scott-vincent/radio-panel/radio-panel/radio.h

#ifndef _RADIO_H_
#define _RADIO_H_

#include "simvars.h"
#include "sevensegment.h"

class radio
{
private:
    SimVars* simVars;
    Aircraft loadedAircraft = UNDEFINED;
    bool airliner = false;
    sevensegment* sevenSegment;

    unsigned char display1[8];
    unsigned char display2[8];
    unsigned char display3[8];
    double activeFreq;
    double standbyFreq;
    int tcasMode = -1;
    int lastTcasMode = -1;
    int transponderState = -1;
    int lastTransponderState = -1;
    int squawk = 0;
    bool showNav = false;
    int usingNav = 0;              // 0 = NAV1, 1 = NAV2, 2 = ADF
    int spoilersVal = INT_MIN;
    int spoilersAutoVal = -6;       // Default to spoilers = retracted
    int spoilersDownVal = 14;
    int lastSpoilersPos = -1;       // 0 = auto, 1 = retracted, 2 = half, 3 = full
    bool gearDown = true;
    bool showSeatBelts = false;
    int receiveAllHideDelay = 0;
    int audioNav1 = 0;
    int audioNav2 = 0;
    int audioAdf = 0;

    // Hardware controls
    int freqWholeControl = -1;
    int freqFracControl = -1;
    int swapControl = -1;
    int comControl = -1;
    int navControl = -1;
    int squawkControl = -1;
    int trimWheelControl = -1;
    int spoilersAutoControl = -1;
    int spoilersPosControl = -1;
    int spoilersDownControl = -1;
    int gearUpControl = -1;
    int gearDownControl = -1;
    int seatBeltsControl = -1;
    int delayedAdfSwap = 0;

    int prevFreqWholeVal = 0;
    int prevFreqFracVal = 0;
    int prevFreqFracPush = 0;
    int fracSetSel = 0;
    int prevSwapPush = 0;
    int prevComPush = 0;
    int prevNavPush = 0;
    int prevSquawkVal = 0;
    int prevSquawkPush = 0;
    int squawkSetSel = 0;
    int prevTrimWheelVal = 0;
    int prevSpoilersAutoToggle = -1;
    int prevSpoilersDownToggle = -1;
    int prevGearUpToggle = -1;
    int prevGearDownToggle = -1;
    int prevFreqWholeValSb;
    int prevFreqFracValSb;
    int prevFreqFracPushSb;
    int prevSwapPushSb = 0;
    int prevComPushSb = 0;
    int prevNavPushSb = 0;
    int prevSquawkValSb = 0;
    int prevSquawkPushSb = 0;

    time_t lastFreqAdjust = 0;
    time_t lastFreqPush = 0;
    time_t lastSquawkAdjust = 0;
    time_t lastSquawkPush = 0;
    time_t lastTcasAdjust = 0;
    time_t now;

public:
    radio();
    void render();
    void update();

private:
    void blankDisplays();
    void writeCom(unsigned char* display, double freq);
    void writeNav(unsigned char* display, double freq);
    void writeAdf(unsigned char* display, double freq);
    void addGpio();
    void gpioFreqWholeInput();
    void gpioFreqFracInput();
    void gpioButtonsInput();
    void gpioSquawkInput();
    void gpioTrimWheelInput();
    void gpioSpoilersInput();
    void gpioGearInput();
    double adjustComWhole(int adjust);
    double adjustComFrac(int adjust);
    double adjustNavWhole(int adjust);
    double adjustNavFrac(int adjust);
    int adjustAdf(double val, int adjust, int setSel);
    int adjustDigit(int val, int adjust);
    int adjustHalfDigit(int val, int adjust);
    int adjustSquawk(int adjust);
    int adjustSquawkDigit(int val, int adjust);
};

#endif // _RADIO_H
